BradypodeHUANG/RK3588-AR-Hearing-Helmet/3D Model/头盔装配 - ELF 2 V1.2-1 ELF 2 V1.2(2)-1 P22-1 61400826021-1 Pin_1-3.STL

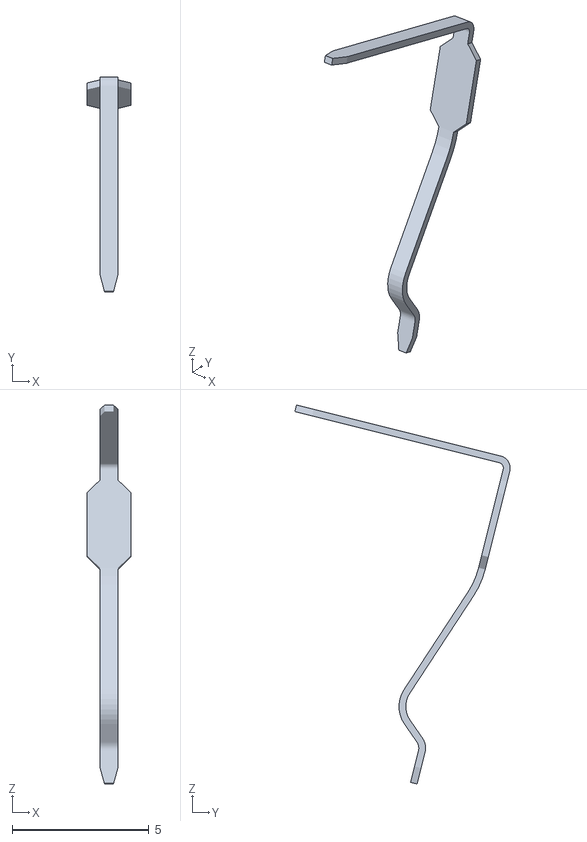
[picture p29: CAD file, 2026-07-08]
3D Model/头盔装配 - ELF 2 V1.2-1 ELF 2 V1.2(2)-1 P22-1 61400826021-1 Pin_1-3.STL
1.60 x 7.86 x 13.8
