BradypodeHUANG/RK3588-AR-Hearing-Helmet/3D Model/头盔装配 - 眼镜整体装配体-1 显示固定（装-2）-眼镜上的-1 显示器1-眼镜上的-1.STL

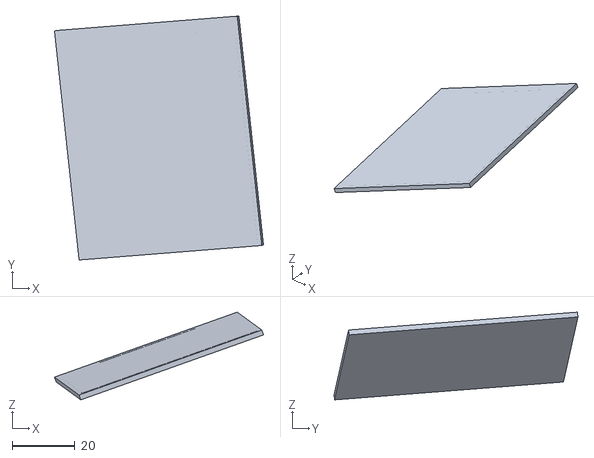
[picture p30: CAD file, 2026-07-08]
3D Model/头盔装配 - 眼镜整体装配体-1 显示固定（装-2）-眼镜上的-1 显示器1-眼镜上的-1.STL
66.6 x 77.8 x 28.0
