BradypodeHUANG/RK3588-AR-Hearing-Helmet/3D Model/头盔装配 - 切半-前-1.STL

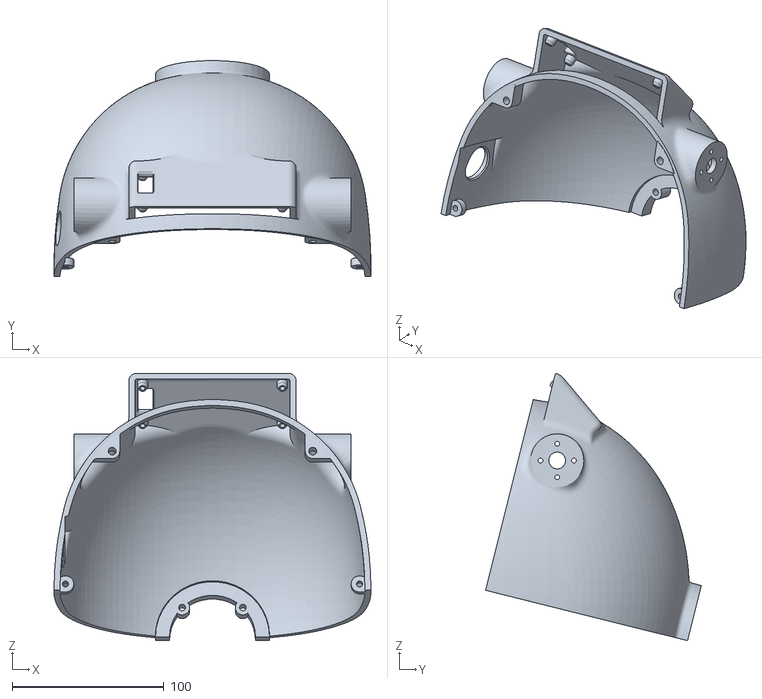
[picture p31: CAD file, 2026-07-08]
3D Model/头盔装配 - 切半-前-1.STL
208.6 x 142.0 x 176.0
