BradypodeHUANG/RK3588-AR-Hearing-Helmet/3D Model/头盔装配 - 眼镜整体装配体-1 上盖-1.STL

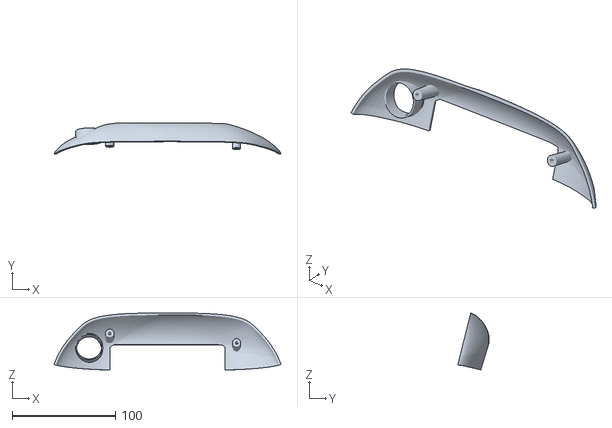
[picture p32: CAD file, 2026-07-08]
3D Model/头盔装配 - 眼镜整体装配体-1 上盖-1.STL
220.1 x 30.5 x 55.2
