BradypodeHUANG/RK3588-AR-Hearing-Helmet/3D Model/头盔装配 - 按键装配体-1 中间-1.STL

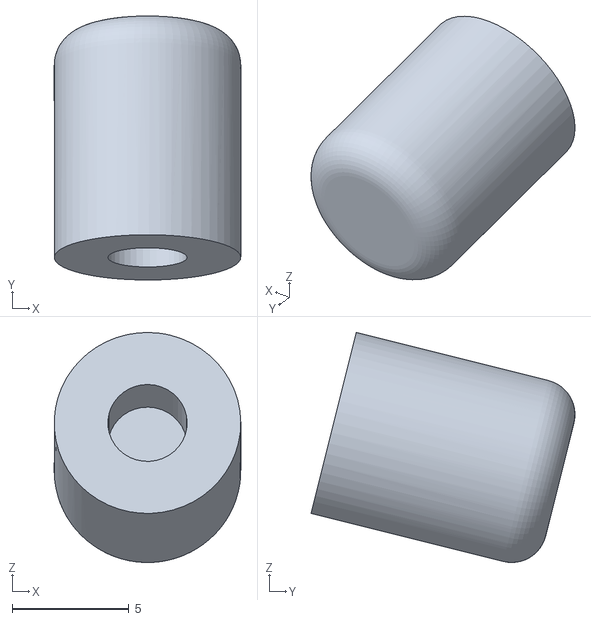
[picture p33: CAD file, 2026-07-08]
3D Model/头盔装配 - 按键装配体-1 中间-1.STL
8.00 x 11.3 x 9.86
