BradypodeHUANG/RK3588-AR-Hearing-Helmet/3D Model/头盔装配 - ELF 2 V1.2-1 ELF 2 V1.2(2)-1 P28-1 0201243-_________2X10P-2.54-1.STL

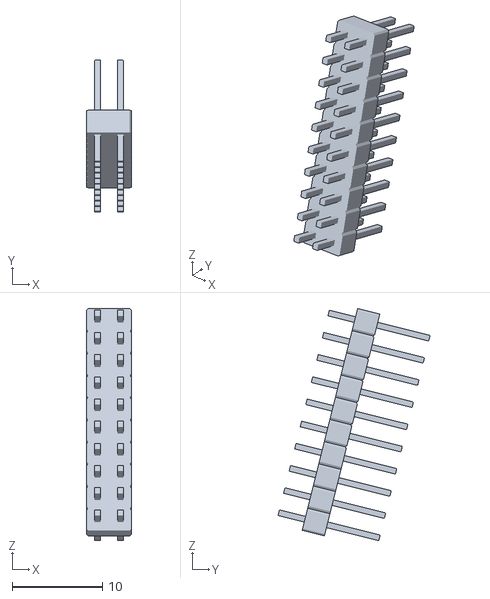
[picture p34: CAD file, 2026-07-08]
3D Model/头盔装配 - ELF 2 V1.2-1 ELF 2 V1.2(2)-1 P28-1 0201243-_________2X10P-2.54-1.STL
5.00 x 16.9 x 25.8
