BradypodeHUANG/RK3588-AR-Hearing-Helmet/3D Model/头盔装配 - 按键装配体-1 按键模块-1 按键模块(2)-1 R1~R0603~R0603~OrpE-3 R0603~R0603~OrpE-1.STL

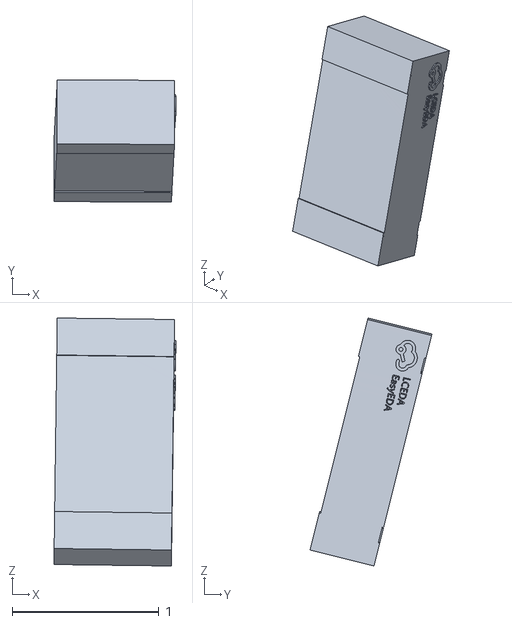
[picture p35: CAD file, 2026-07-08]
3D Model/头盔装配 - 按键装配体-1 按键模块-1 按键模块(2)-1 R1~R0603~R0603~OrpE-3 R0603~R0603~OrpE-1.STL
0.83 x 0.832 x 1.69
