BradypodeHUANG/RK3588-AR-Hearing-Helmet/3D Model/头盔装配 - 驱动电路板-1.STL

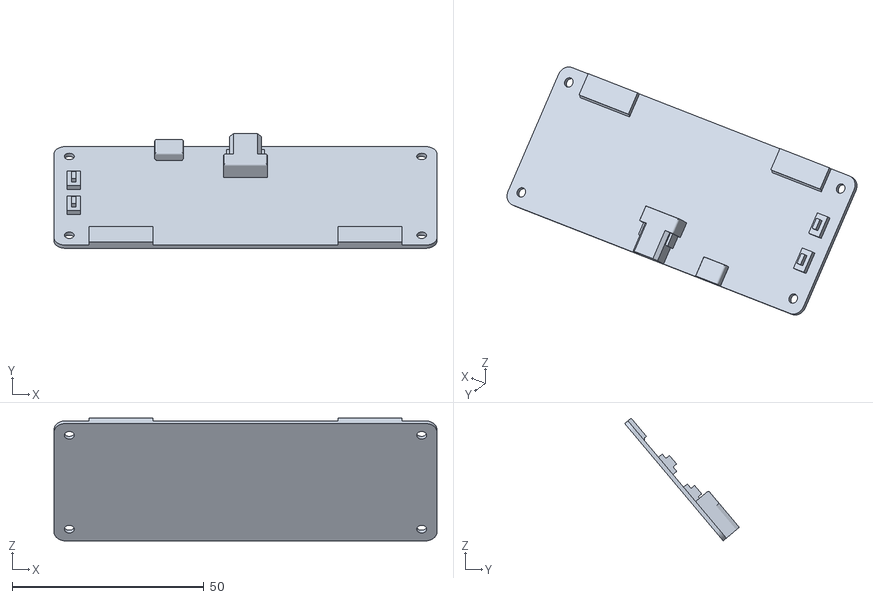
[picture p36: CAD file, 2026-07-08]
3D Model/头盔装配 - 驱动电路板-1.STL
100.0 x 29.9 x 32.1
