BradypodeHUANG/RK3588-AR-Hearing-Helmet/3D Model/头盔装配 - 前后链接-1.STL

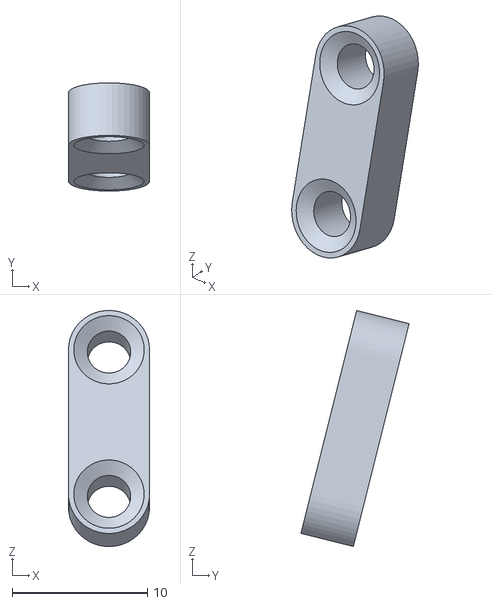
[picture p37: CAD file, 2026-07-08]
3D Model/头盔装配 - 前后链接-1.STL
6.00 x 8.00 x 17.4
