BradypodeHUANG/RK3588-AR-Hearing-Helmet/3D Model/头盔装配 - ELF 2 V1.2-1 ELF 2 V1.2(2)-1 P22-1 61400826021-1 Shielding_3-1.STL

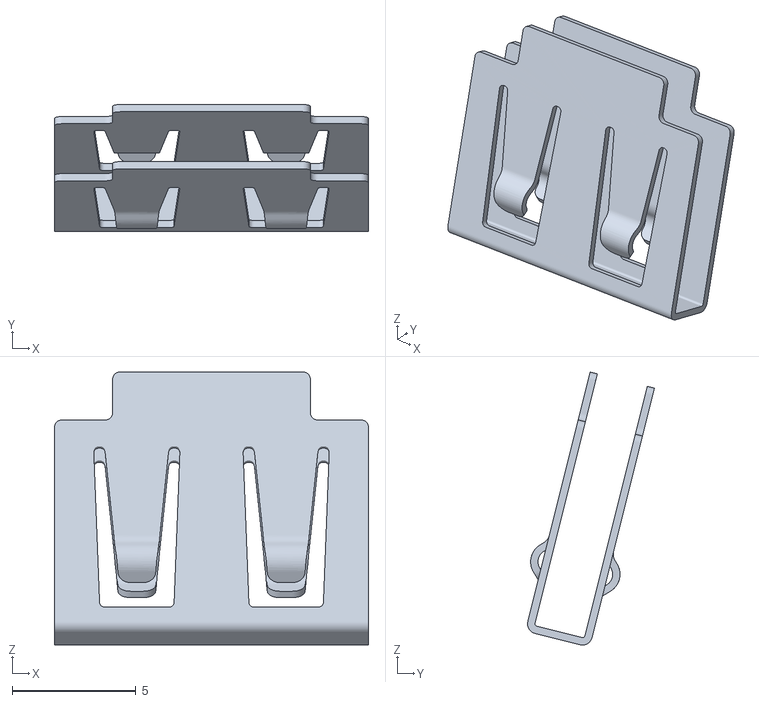
[picture p38: CAD file, 2026-07-08]
3D Model/头盔装配 - ELF 2 V1.2-1 ELF 2 V1.2(2)-1 P22-1 61400826021-1 Shielding_3-1.STL
12.7 x 5.13 x 11.0
