BradypodeHUANG/RK3588-AR-Hearing-Helmet/3D Model/头盔装配 - 按键装配体-1 按键模块-1 按键模块(2)-1 SW2~KEY-SMD_4P-__SMD_4P-L6.0-W6.0-H5.0-LS10.0-P4.5~OrpE-1.STL

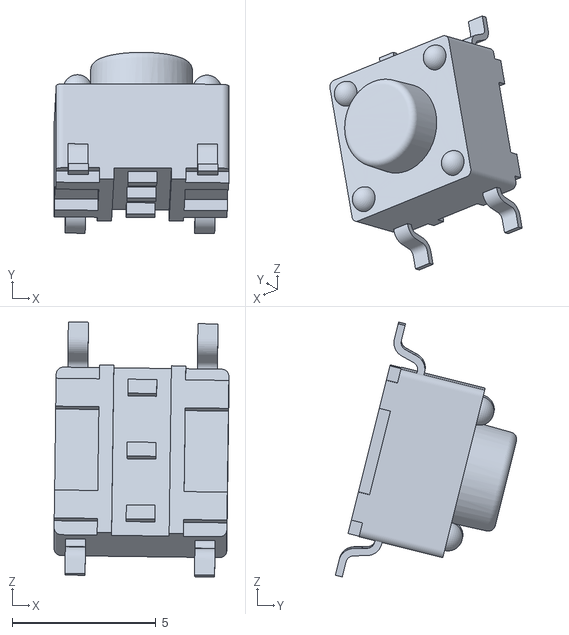
[picture p39: CAD file, 2026-07-08]
3D Model/头盔装配 - 按键装配体-1 按键模块-1 按键模块(2)-1 SW2~KEY-SMD_4P-__SMD_4P-L6.0-W6.0-H5.0-LS10.0-P4.5~OrpE-1.STL
6.07 x 6.30 x 8.86
