BradypodeHUANG/RK3588-AR-Hearing-Helmet/3D Model/头盔装配 - 固定圆环-1.STL

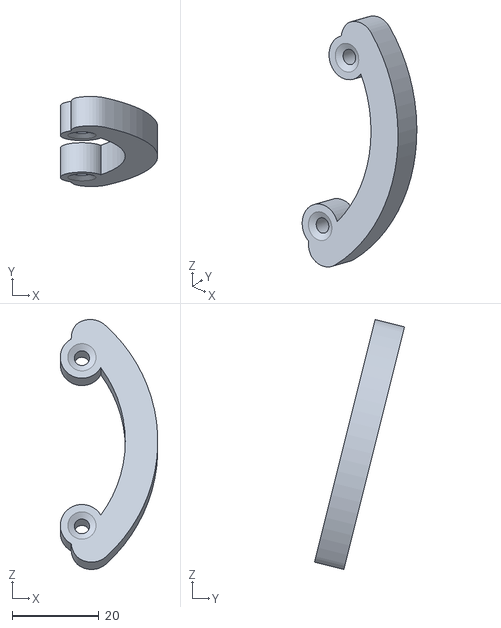
[picture p40: CAD file, 2026-07-08]
3D Model/头盔装配 - 固定圆环-1.STL
22.5 x 20.8 x 57.7
