BradypodeHUANG/RK3588-AR-Hearing-Helmet/3D Model/头盔装配 - 喇叭-1.STL

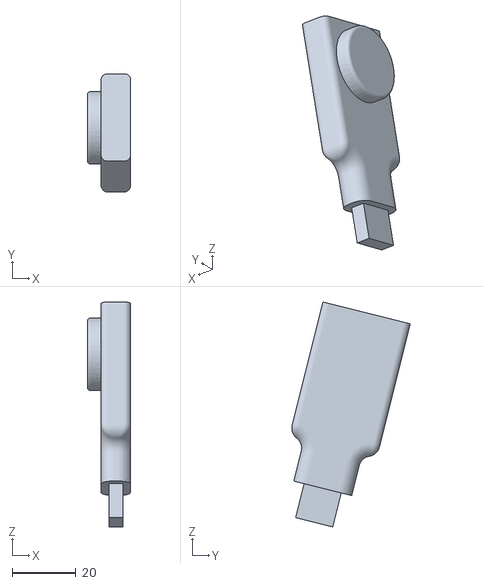
[picture p41: CAD file, 2026-07-08]
3D Model/头盔装配 - 喇叭-1.STL
13.6 x 37.1 x 70.5
