BradypodeHUANG/RK3588-AR-Hearing-Helmet/3D Model/头盔装配 - ELF 2 V1.2-1 ELF 2 V1.2(2)-1 P14-1 0103021-_____ - 26P-1.STL

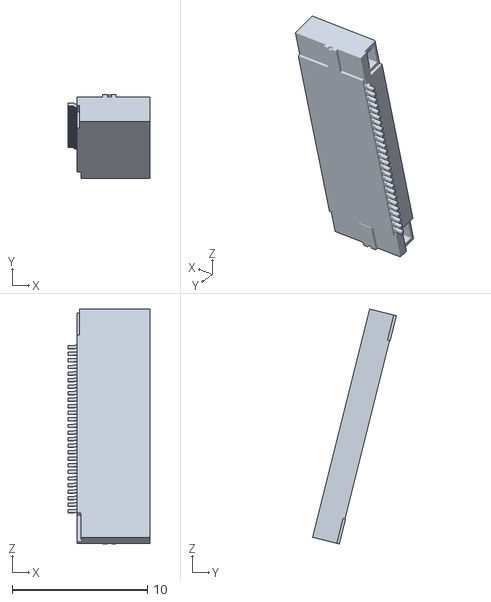
[picture p42: CAD file, 2026-07-08]
3D Model/头盔装配 - ELF 2 V1.2-1 ELF 2 V1.2(2)-1 P14-1 0103021-_____ - 26P-1.STL
6.05 x 6.20 x 17.4
