BradypodeHUANG/RK3588-AR-Hearing-Helmet/3D Model/头盔装配 - 连杆-1-2.STL

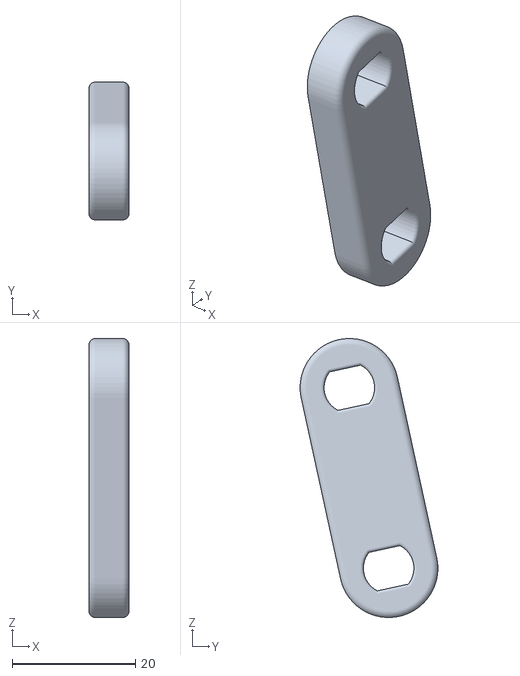
[picture p43: CAD file, 2026-07-08]
3D Model/头盔装配 - 连杆-1-2.STL
6.50 x 22.4 x 45.3
