BradypodeHUANG/RK3588-AR-Hearing-Helmet/3D Model/头盔装配 - 按键装配体-1 按键模块-1 按键模块(2)-1 SW1~SW-SMD_L3.9__P4.45~SW-SMD_L3.9-W2.9-H2.0-LS4.8~OrpE-1.STL

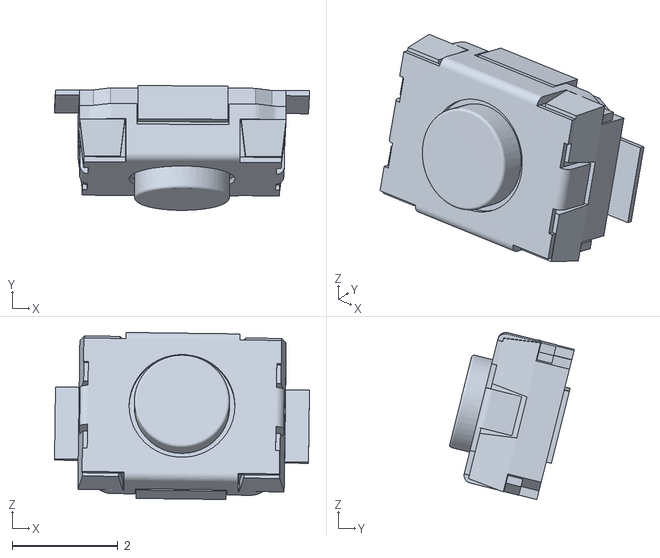
[picture p44: CAD file, 2026-07-08]
3D Model/头盔装配 - 按键装配体-1 按键模块-1 按键模块(2)-1 SW1~SW-SMD_L3.9__P4.45~SW-SMD_L3.9-W2.9-H2.0-LS4.8~OrpE-1.STL
4.82 x 2.36 x 3.16
