BradypodeHUANG/RK3588-AR-Hearing-Helmet/3D Model/头盔装配 - 连杆-2-2.STL

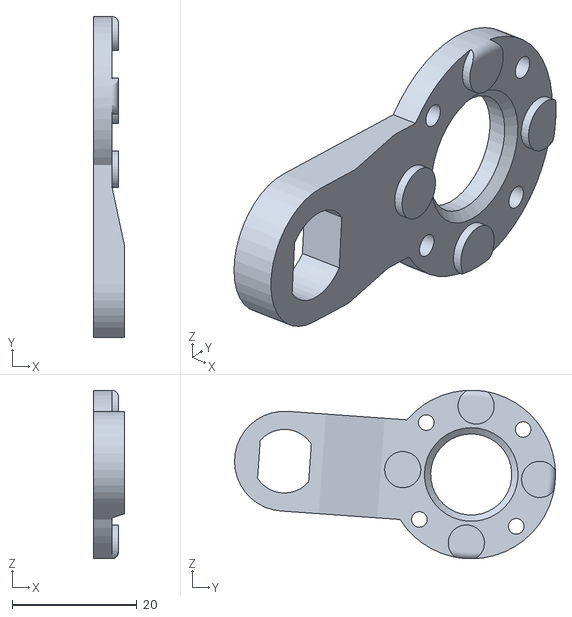
[picture p45: CAD file, 2026-07-08]
3D Model/头盔装配 - 连杆-2-2.STL
5.00 x 51.4 x 27.0
