BradypodeHUANG/RK3588-AR-Hearing-Helmet/3D Model/头盔装配 - 眼镜整体装配体-1 镜片1-眼镜上的-1.STL

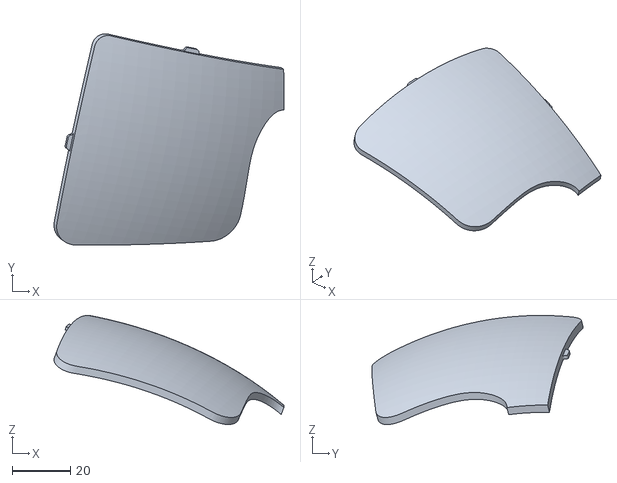
[picture p46: CAD file, 2026-07-08]
3D Model/头盔装配 - 眼镜整体装配体-1 镜片1-眼镜上的-1.STL
79.1 x 72.7 x 37.5
