BradypodeHUANG/RK3588-AR-Hearing-Helmet/3D Model/头盔装配 - 按键装配体-1 外围-2.STL

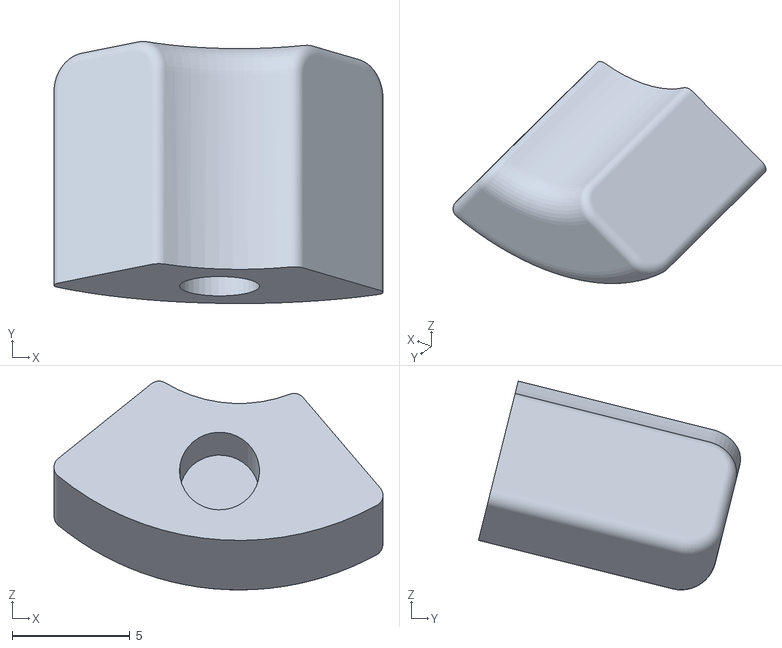
[picture p47: CAD file, 2026-07-08]
3D Model/头盔装配 - 按键装配体-1 外围-2.STL
14.0 x 11.1 x 8.88
