BradypodeHUANG/RK3588-AR-Hearing-Helmet/3D Model/头盔装配 - ELF 2 V1.2-1 ELF 2 V1.2(2)-1 P8-1 1841902_1932258-1-1.STL

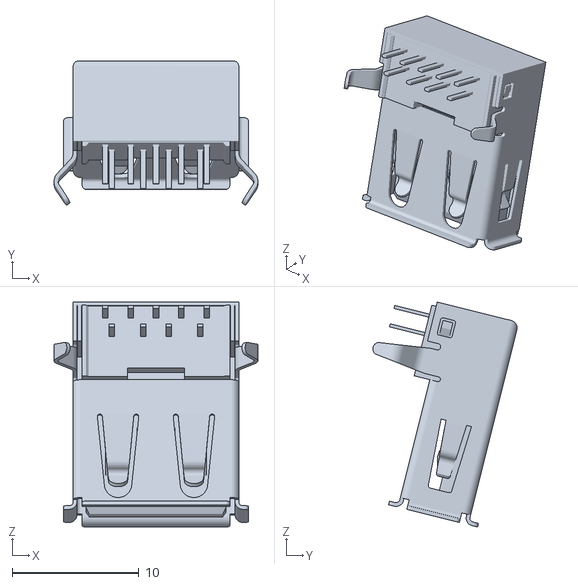
[picture p48: CAD file, 2026-07-08]
3D Model/头盔装配 - ELF 2 V1.2-1 ELF 2 V1.2(2)-1 P8-1 1841902_1932258-1-1.STL
16.1 x 11.4 x 17.8
