BradypodeHUANG/RK3588-AR-Hearing-Helmet/3D Model/头盔装配 - 按键装配体-1 按键模块-1 按键模块(2)-1 LED1~LED0603-RD__3-RD~OrpE-1 LED0603-RD~LED0603-RD~OrpE-1.STL

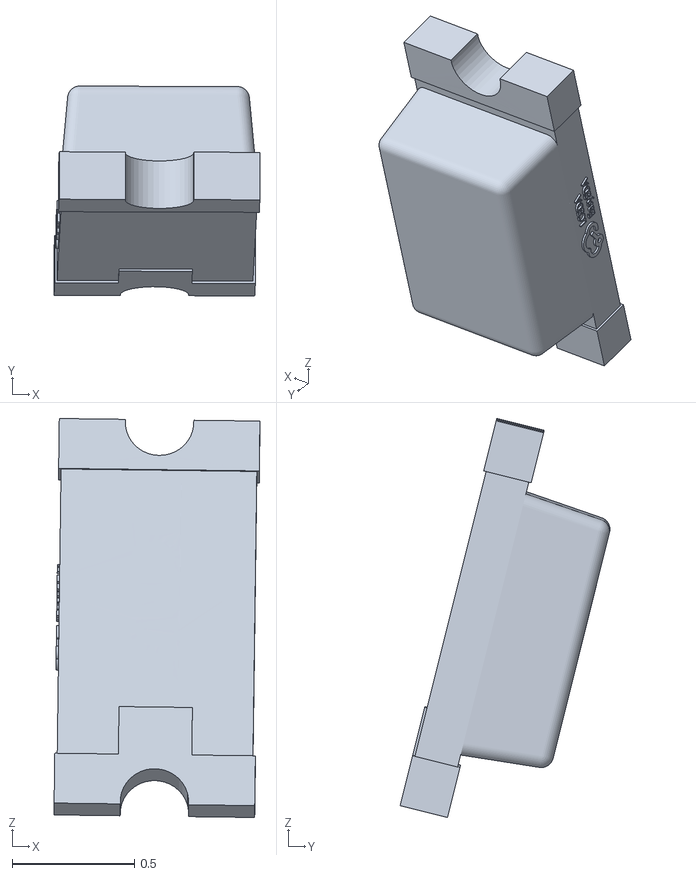
[picture p50: CAD file, 2026-07-08]
3D Model/头盔装配 - 按键装配体-1 按键模块-1 按键模块(2)-1 LED1~LED0603-RD__3-RD~OrpE-1 LED0603-RD~LED0603-RD~OrpE-1.STL
0.841 x 0.858 x 1.63
