BradypodeHUANG/RK3588-AR-Hearing-Helmet/3D Model/头盔装配 - ELF 2 V1.2-1 ELF 2 V1.2(2)-1 Free-Models__ocket_RGB16777215-1 HDMI_socket_inside-1.STL

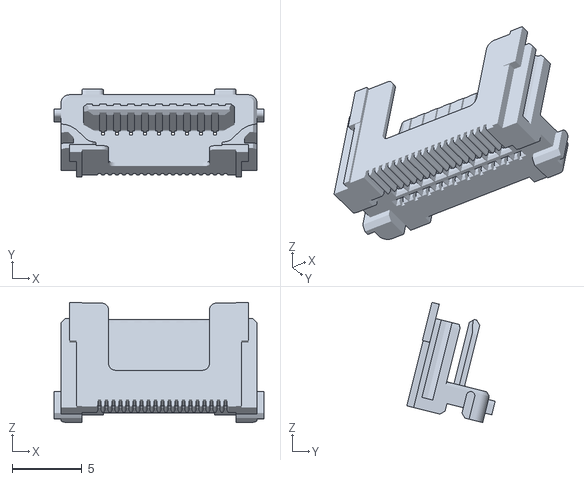
[picture p51: CAD file, 2026-07-08]
3D Model/头盔装配 - ELF 2 V1.2-1 ELF 2 V1.2(2)-1 Free-Models__ocket_RGB16777215-1 HDMI_socket_inside-1.STL
15.0 x 6.32 x 8.59
