BradypodeHUANG/RK3588-AR-Hearing-Helmet/3D Model/头盔装配 - 阻力转轴-2.STL

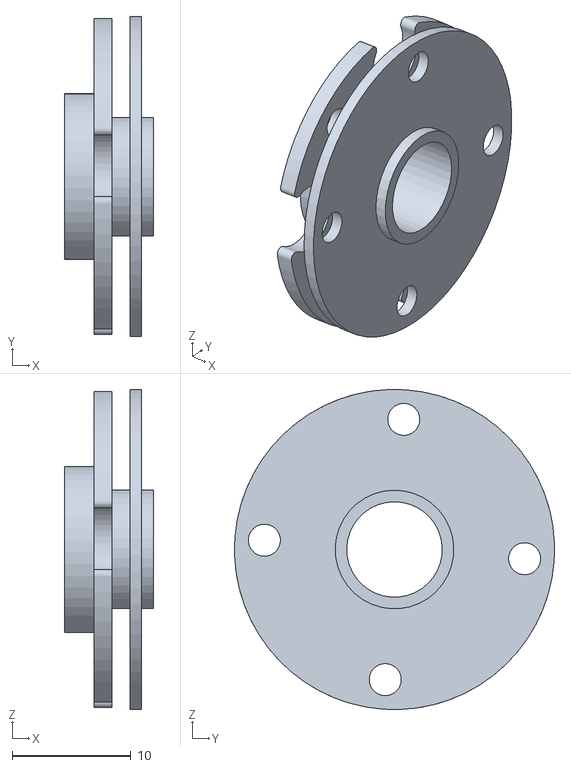
[picture p52: CAD file, 2026-07-08]
3D Model/头盔装配 - 阻力转轴-2.STL
7.50 x 27.0 x 27.0
