BradypodeHUANG/RK3588-AR-Hearing-Helmet/3D Model/头盔装配 - 眼镜整体装配体-1 额头挡头-眼镜上的-1.STL

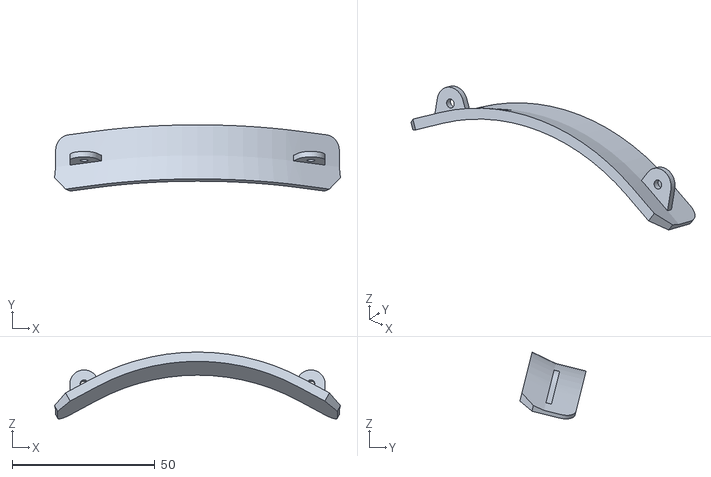
[picture p53: CAD file, 2026-07-08]
3D Model/头盔装配 - 眼镜整体装配体-1 额头挡头-眼镜上的-1.STL
100.3 x 23.2 x 23.5
