BradypodeHUANG/RK3588-AR-Hearing-Helmet/3D Model/头盔装配 - 眼镜整体装配体-1 骨架-1.STL

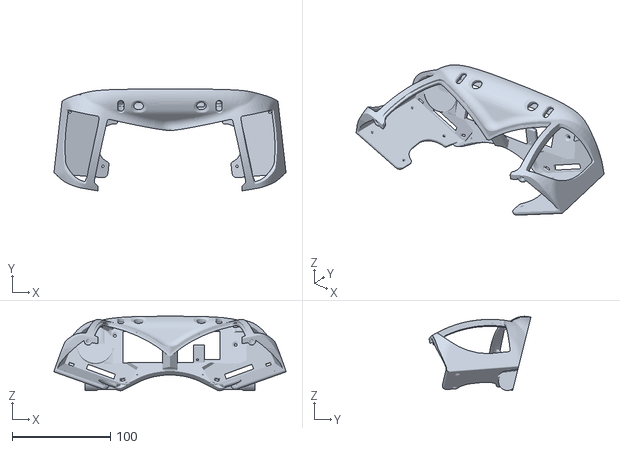
[picture p54: CAD file, 2026-07-08]
3D Model/头盔装配 - 眼镜整体装配体-1 骨架-1.STL
236.5 x 103.9 x 76.0
