BradypodeHUANG/RK3588-AR-Hearing-Helmet/3D Model/头盔装配 - ELF 2 V1.2-1 ELF 2 V1.2(2)-1 Free-Models__socket_RGB16777215-1 HDMI_socket_cover-1.STL

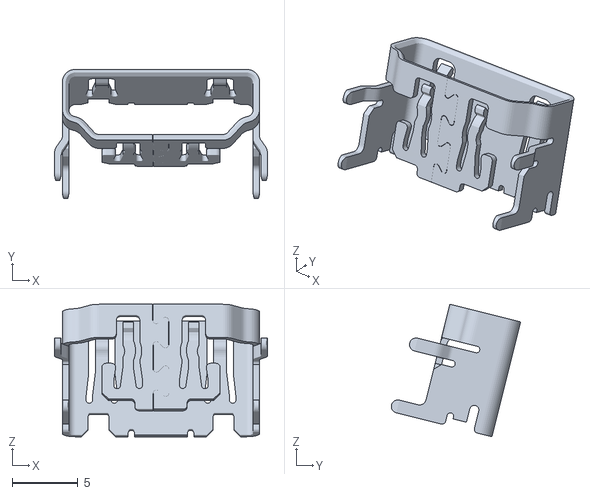
[picture p55: CAD file, 2026-07-08]
3D Model/头盔装配 - ELF 2 V1.2-1 ELF 2 V1.2(2)-1 Free-Models__socket_RGB16777215-1 HDMI_socket_cover-1.STL
16.2 x 9.84 x 10.1
