BradypodeHUANG/RK3588-AR-Hearing-Helmet/3D Model/头盔装配 - ELF 2 V1.2-1 ELF 2 V1.2(2)-1 P11-1 1120104005-TF-______-1.STL

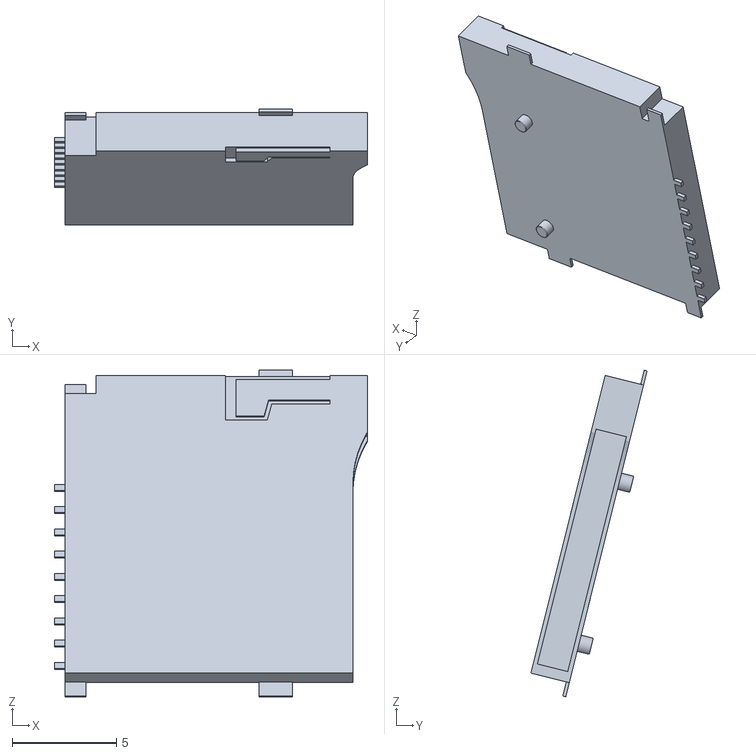
[picture p56: CAD file, 2026-07-08]
3D Model/头盔装配 - ELF 2 V1.2-1 ELF 2 V1.2(2)-1 P11-1 1120104005-TF-______-1.STL
15.0 x 5.58 x 15.7
