BradypodeHUANG/RK3588-AR-Hearing-Helmet/3D Model/头盔装配 - ELF 2 V1.2-1 ELF 2 V1.2(2)-1 P13-1 1120202139-______RJ45-Gigabit-2139-1.STL

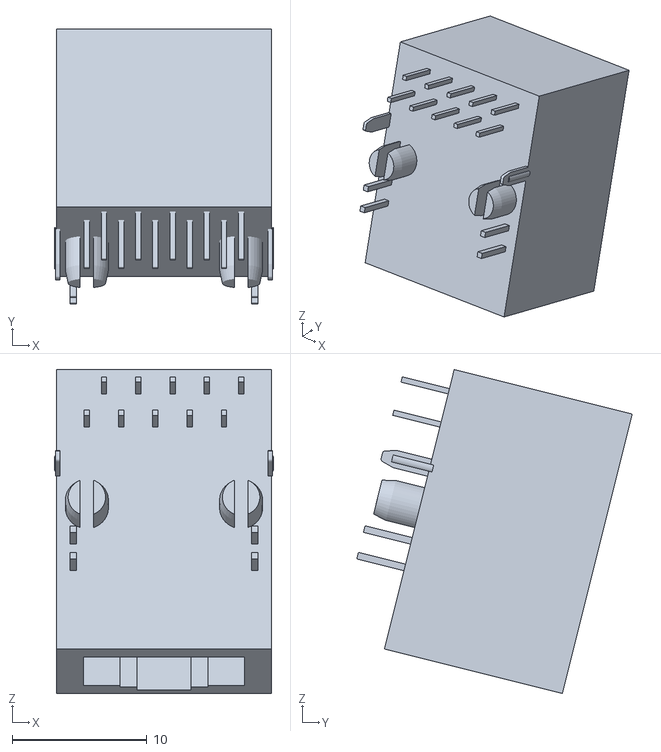
[picture p57: CAD file, 2026-07-08]
3D Model/头盔装配 - ELF 2 V1.2-1 ELF 2 V1.2(2)-1 P13-1 1120202139-______RJ45-Gigabit-2139-1.STL
16.2 x 20.4 x 24.0
