BradypodeHUANG/RK3588-AR-Hearing-Helmet/3D Model/头盔装配 - ELF 2 V1.2-1 ELF 2 V1.2(2)-1 P19-1 0201007-____________-2P-1.STL

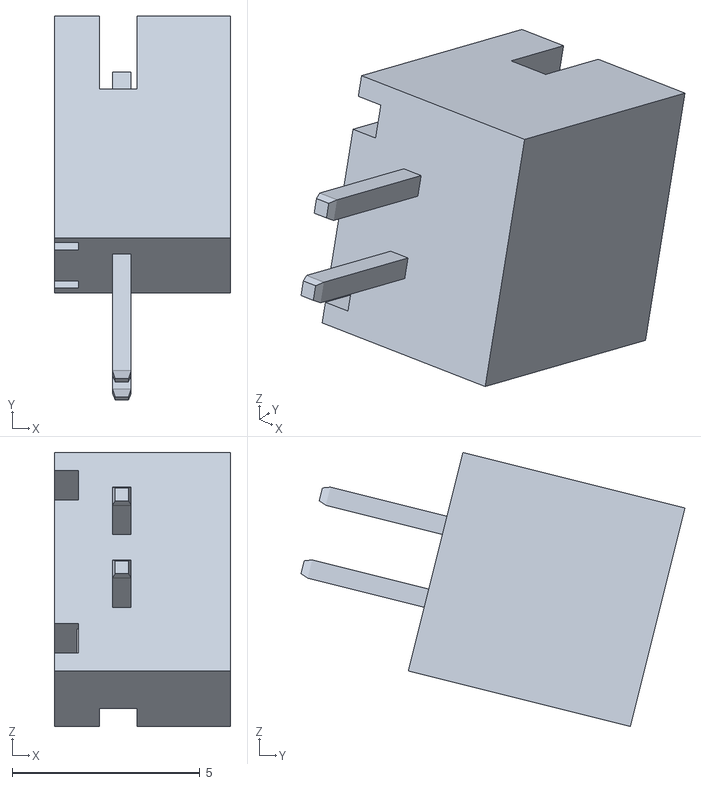
[picture p58: CAD file, 2026-07-08]
3D Model/头盔装配 - ELF 2 V1.2-1 ELF 2 V1.2(2)-1 P19-1 0201007-____________-2P-1.STL
4.70 x 10.2 x 7.30
