BradypodeHUANG/RK3588-AR-Hearing-Helmet/3D Model/头盔装配 - 麦克风装配图-1 麦克风阵列-1.STL

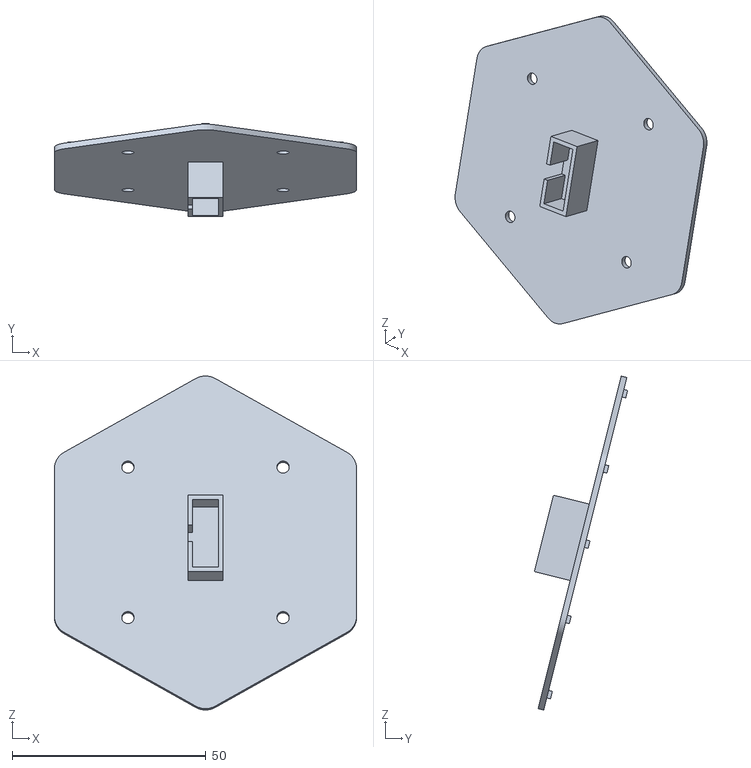
[picture p59: CAD file, 2026-07-08]
3D Model/头盔装配 - 麦克风装配图-1 麦克风阵列-1.STL
77.9 x 24.0 x 86.1
