BradypodeHUANG/RK3588-AR-Hearing-Helmet/3D Model/头盔装配 - 按键装配体-1 按键模块-1 HDR-TH_2P-P2.54-V-M~HDR2.54-M-LI-1X2P~OrpE-1.STL

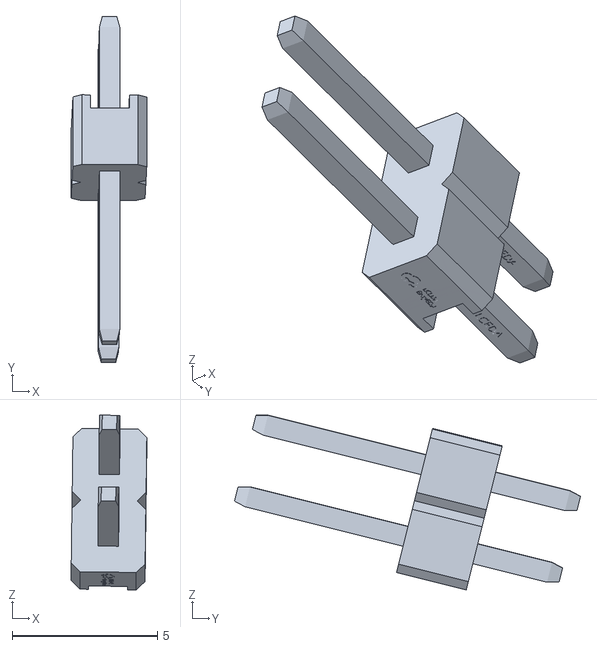
[picture p60: CAD file, 2026-07-08]
3D Model/头盔装配 - 按键装配体-1 按键模块-1 HDR-TH_2P-P2.54-V-M~HDR2.54-M-LI-1X2P~OrpE-1.STL
2.60 x 11.9 x 6.01
