BradypodeHUANG/RK3588-AR-Hearing-Helmet/3D Model/头盔装配 - ELF 2 V1.2-1 ELF 2 V1.2(2)-1 P15-1 0103013-_____ - 30P-1.STL

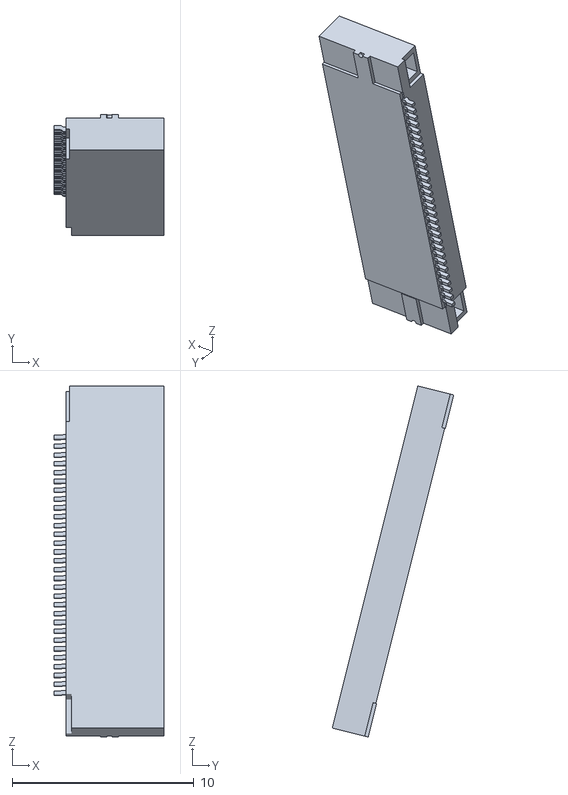
[picture p61: CAD file, 2026-07-08]
3D Model/头盔装配 - ELF 2 V1.2-1 ELF 2 V1.2(2)-1 P15-1 0103013-_____ - 30P-1.STL
6.05 x 6.68 x 19.3
