BradypodeHUANG/RK3588-AR-Hearing-Helmet/3D Model/头盔装配 - ELF 2 V1.2-1 ELF 2 V1.2(2)-1 P22-1 61400826021-1 Insulator-1.STL

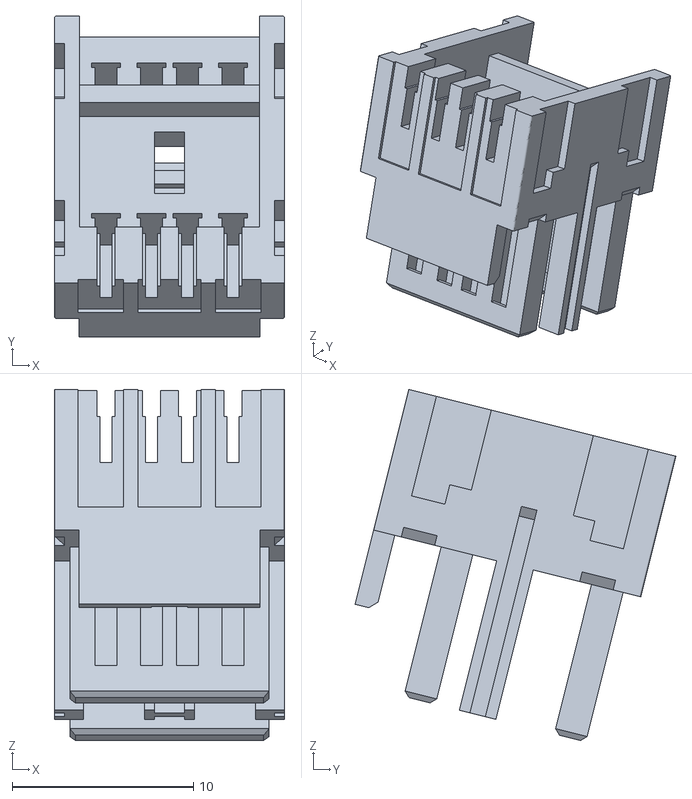
[picture p62: CAD file, 2026-07-08]
3D Model/头盔装配 - ELF 2 V1.2-1 ELF 2 V1.2(2)-1 P22-1 61400826021-1 Insulator-1.STL
12.7 x 17.7 x 19.4
