BradypodeHUANG/RK3588-AR-Hearing-Helmet/3D Model/头盔装配 - 切半-后-1.STL

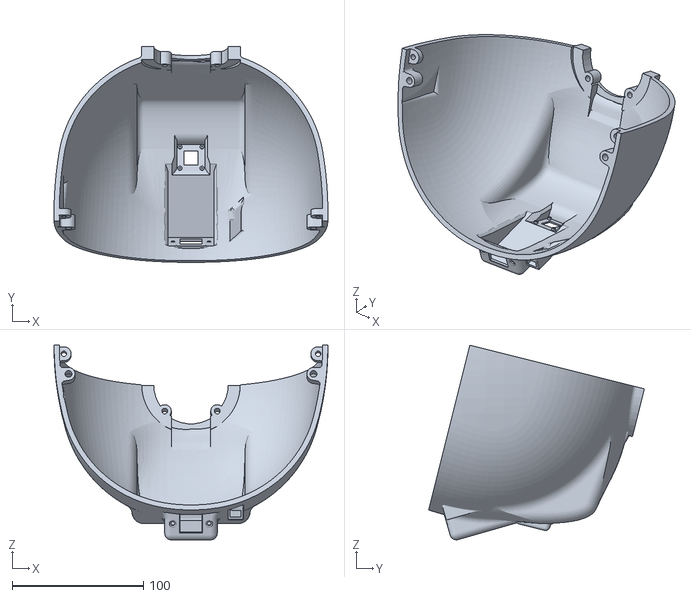
[picture p63: CAD file, 2026-07-08]
3D Model/头盔装配 - 切半-后-1.STL
208.6 x 164.3 x 148.2
