BradypodeHUANG/RK3588-AR-Hearing-Helmet/3D Model/头盔装配 - 眼镜整体装配体-1 3D摄像头-眼镜上的-1.STL

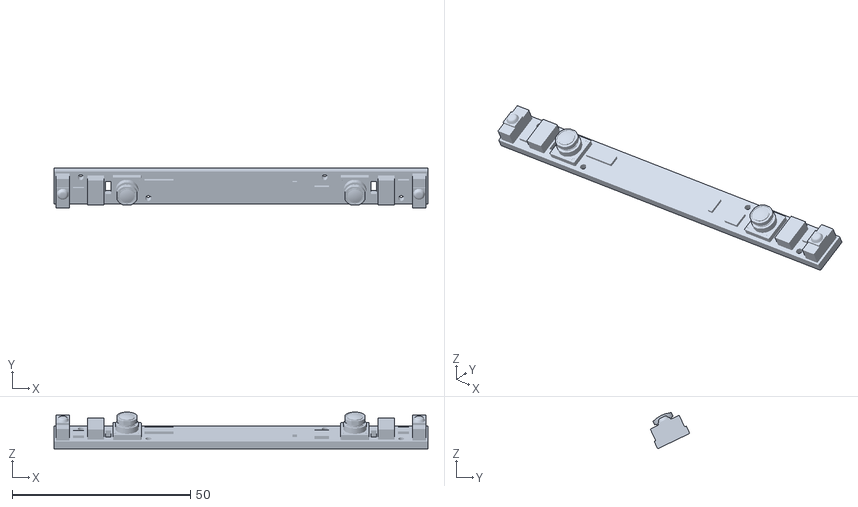
[picture p64: CAD file, 2026-07-08]
3D Model/头盔装配 - 眼镜整体装配体-1 3D摄像头-眼镜上的-1.STL
105.0 x 11.1 x 10.3
