BradypodeHUANG/RK3588-AR-Hearing-Helmet/3D Model/头盔装配 - ELF 2 V1.2-1 ELF 2 V1.2(2)-1 P9-1 1120201188-3D____-APCI0085_-1.STL

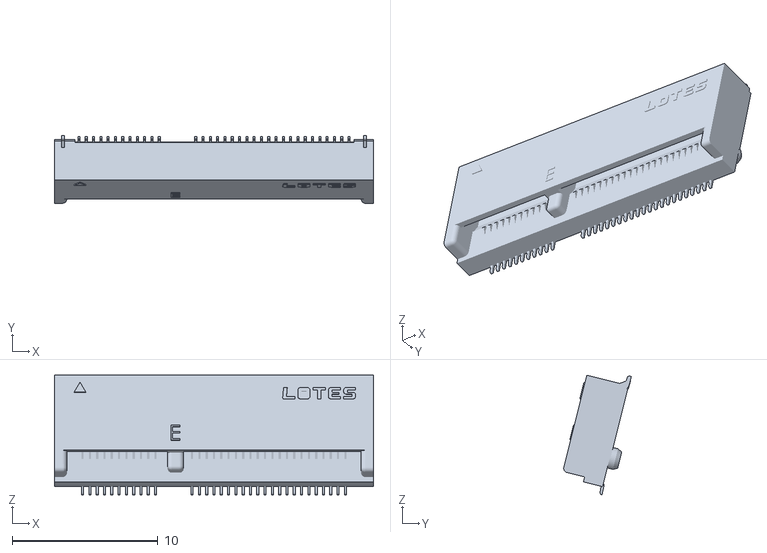
[picture p65: CAD file, 2026-07-08]
3D Model/头盔装配 - ELF 2 V1.2-1 ELF 2 V1.2(2)-1 P9-1 1120201188-3D____-APCI0085_-1.STL
21.8 x 4.63 x 8.20
