BradypodeHUANG/RK3588-AR-Hearing-Helmet/3D Model/头盔装配 - ELF 2 V1.2-1 Board~1hJp-2.STL

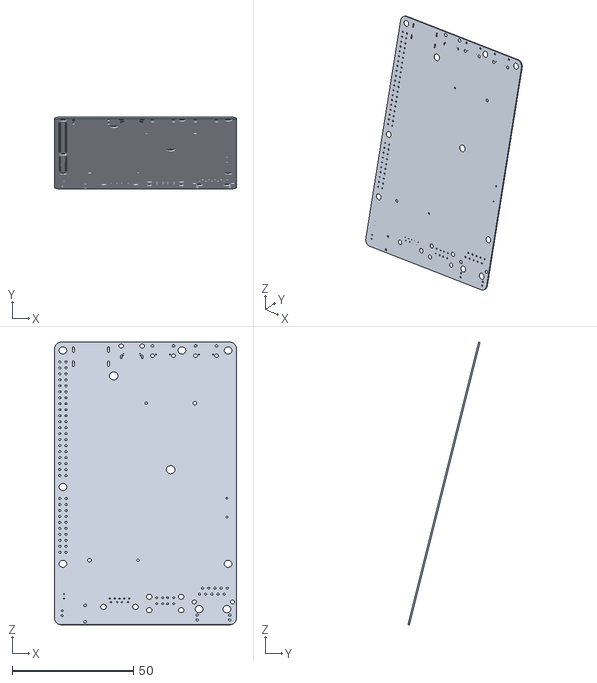
[picture p66: CAD file, 2026-07-08]
3D Model/头盔装配 - ELF 2 V1.2-1 Board~1hJp-2.STL
75.0 x 29.7 x 116.5
