BradypodeHUANG/RK3588-AR-Hearing-Helmet/3D Model/头盔装配 - ELF 2 V1.2-1 ELF 2 V1.2(2)-1 P22-1 61400826021-1 Shielding-1.STL

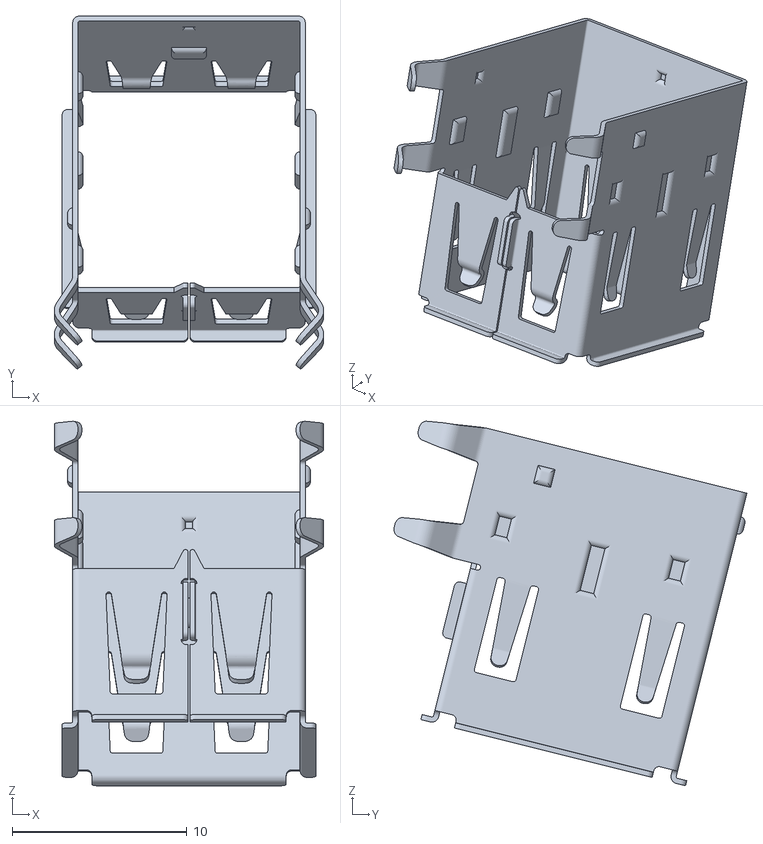
[picture p67: CAD file, 2026-07-08]
3D Model/头盔装配 - ELF 2 V1.2-1 ELF 2 V1.2(2)-1 P22-1 61400826021-1 Shielding-1.STL
15.4 x 20.2 x 20.8
