BradypodeHUANG/RK3588-AR-Hearing-Helmet/3D Model/头盔装配 - 按键装配体-1 按键模块-1 按键模块(2)-1 H2~HDR-TH_4P-P2__.54-V-M~HDR-TH_4P-P2.54-M-LI-1X4P~OrpE-1.STL

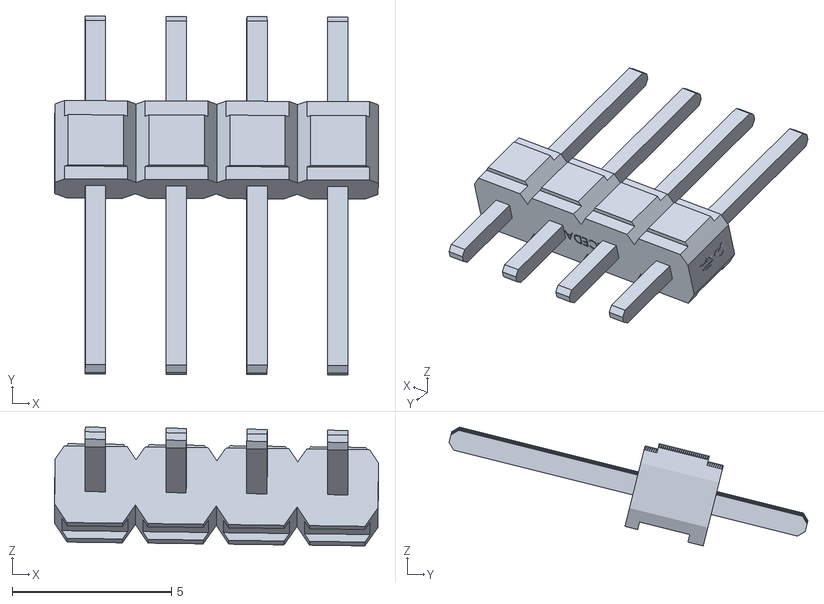
[picture p68: CAD file, 2026-07-08]
3D Model/头盔装配 - 按键装配体-1 按键模块-1 按键模块(2)-1 H2~HDR-TH_4P-P2__.54-V-M~HDR-TH_4P-P2.54-M-LI-1X4P~OrpE-1.STL
10.2 x 11.3 x 3.74
