BradypodeHUANG/RK3588-AR-Hearing-Helmet/3D Model/头盔装配 - ELF 2 V1.2-1 ELF 2 V1.2(2)-1 P24-1 1120201185-3D____-APCI0107-1.STL

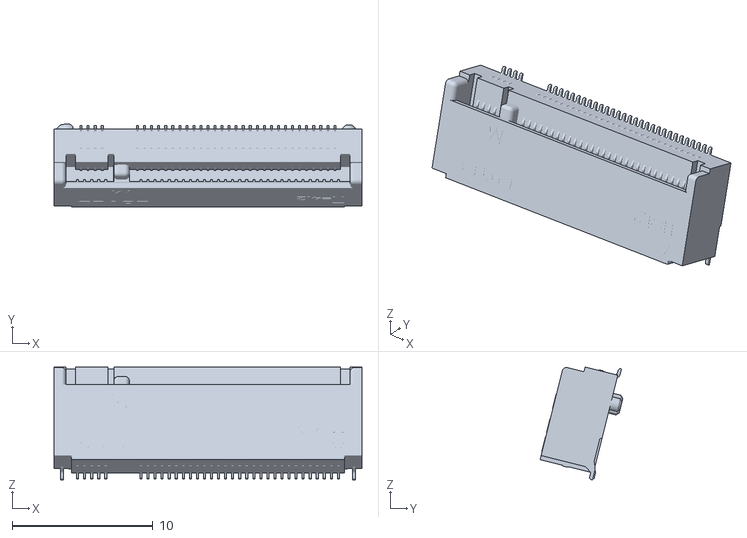
[picture p69: CAD file, 2026-07-08]
3D Model/头盔装配 - ELF 2 V1.2-1 ELF 2 V1.2(2)-1 P24-1 1120201185-3D____-APCI0107-1.STL
21.8 x 5.88 x 8.02
