BradypodeHUANG/RK3588-AR-Hearing-Helmet/3D Model/头盔装配 - 麦克风装配图-1 转接板-1.STL

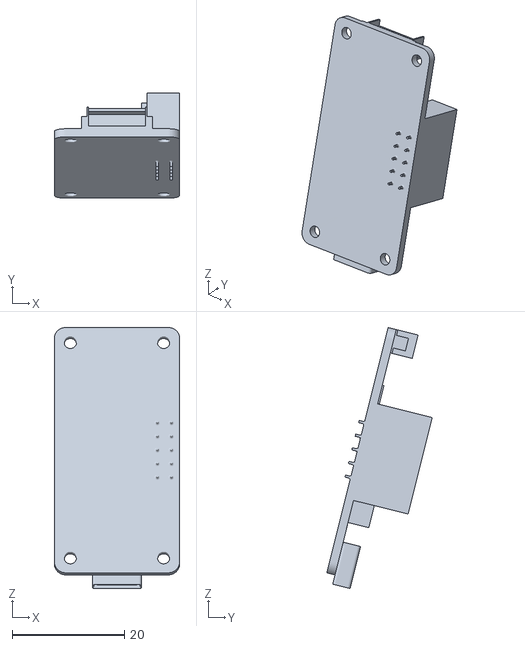
[picture p70: CAD file, 2026-07-08]
3D Model/头盔装配 - 麦克风装配图-1 转接板-1.STL
22.3 x 18.8 x 46.4
